prashant87/Self-Balancing-Robot-on-Tiva-C-TM4C-Dev-KIT/Mechanical/Robot Frame Base/Pin2s.SLDPRT

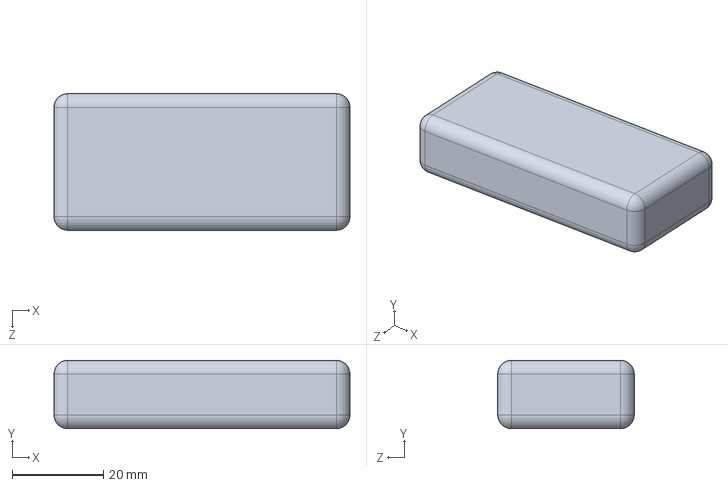
[picture p19: CAD file, 2020-07-25]
Mechanical/Robot Frame Base/Pin2s.SLDPRT
65.0 x 15.0 x 30.0 mm
