prashant87/Self-Balancing-Robot-on-Tiva-C-TM4C-Dev-KIT/Mechanical/Robot Frame Base/Mạch TT.SLDPRT

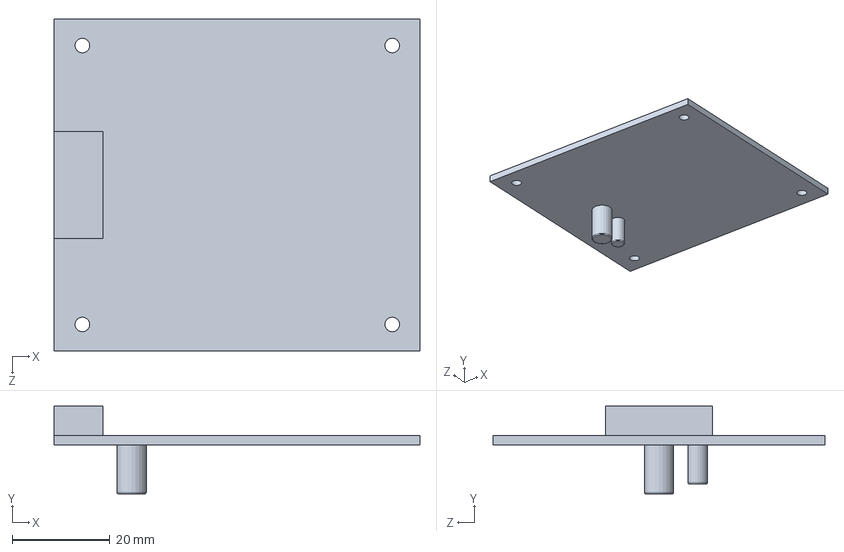
[picture p20: CAD file, 2020-07-25]
Mechanical/Robot Frame Base/Mạch TT.SLDPRT
75.0 x 18.0 x 68.0 mm
