prashant87/Self-Balancing-Robot-on-Tiva-C-TM4C-Dev-KIT/Mechanical/Robot Frame Base/Trụ6.SLDPRT

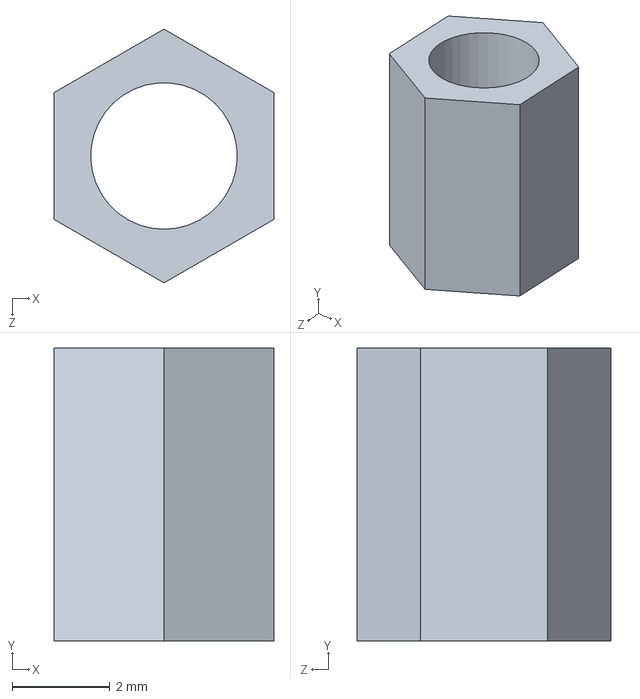
[picture p21: CAD file, 2020-07-25]
Mechanical/Robot Frame Base/Trụ6.SLDPRT
4.50 x 6.00 x 5.20 mm
