prashant87/Self-Balancing-Robot-on-Tiva-C-TM4C-Dev-KIT/Mechanical/Robot Frame Base/Bánh xe.SLDPRT

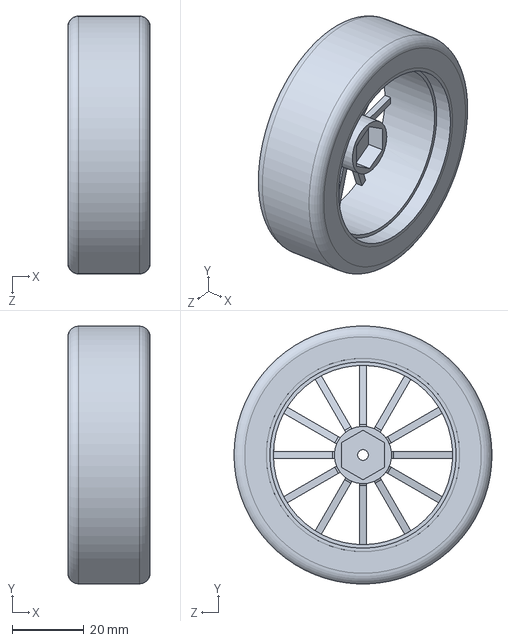
[picture p22: CAD file, 2020-07-25]
Mechanical/Robot Frame Base/Bánh xe.SLDPRT
23.0 x 71.9 x 72.0 mm
