prashant87/Self-Balancing-Robot-on-Tiva-C-TM4C-Dev-KIT/Mechanical/Robot Frame Base/Base4.SLDPRT

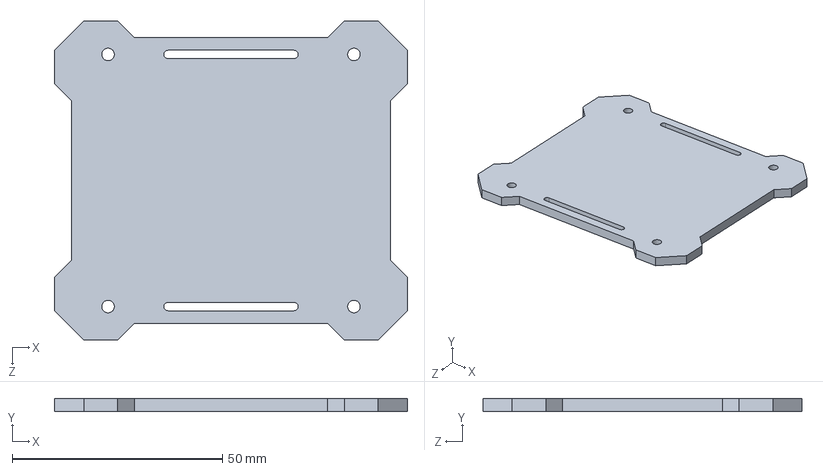
[picture p23: CAD file, 2020-07-25]
Mechanical/Robot Frame Base/Base4.SLDPRT
84.0 x 3.00 x 76.0 mm
