prashant87/Self-Balancing-Robot-on-Tiva-C-TM4C-Dev-KIT/Mechanical/Robot Frame Base/Cầu H.SLDPRT

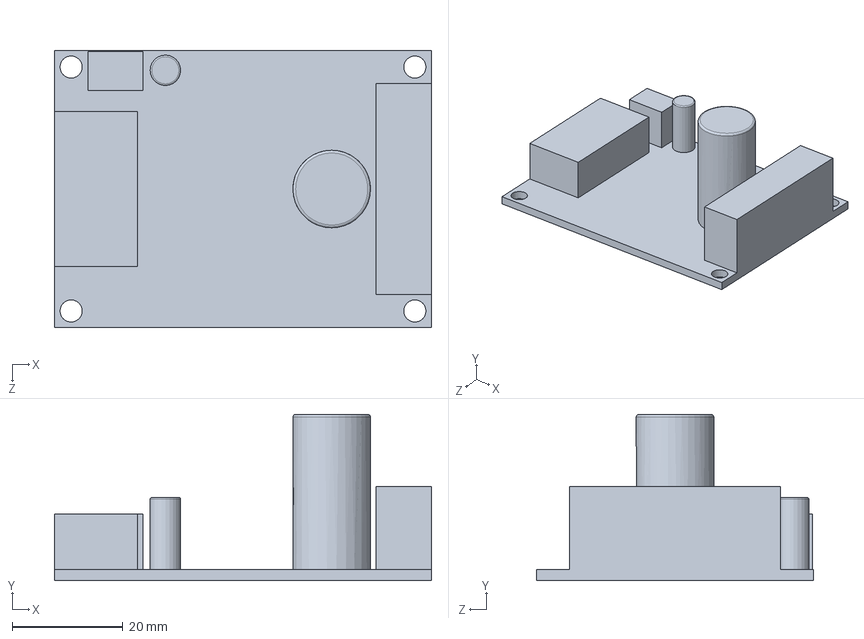
[picture p24: CAD file, 2020-07-25]
Mechanical/Robot Frame Base/Cầu H.SLDPRT
68.0 x 30.0 x 50.0 mm
