prashant87/Self-Balancing-Robot-on-Tiva-C-TM4C-Dev-KIT/Mechanical/Robot Frame Base/IMU_Quick.SLDPRT

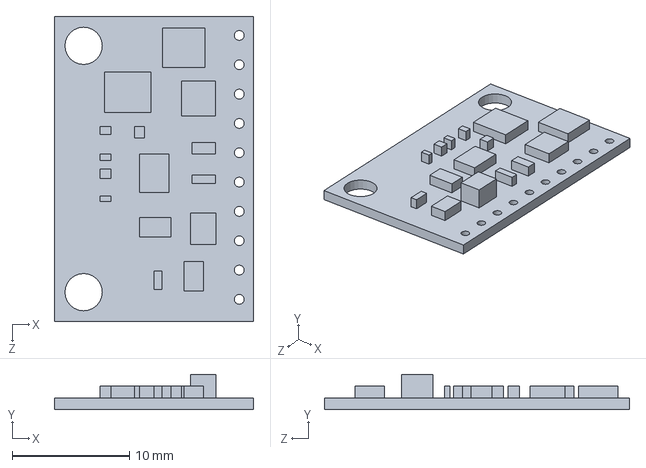
[picture p25: CAD file, 2020-07-25]
Mechanical/Robot Frame Base/IMU_Quick.SLDPRT
17.0 x 3.00 x 26.0 mm
