prashant87/Self-Balancing-Robot-on-Tiva-C-TM4C-Dev-KIT/Mechanical/Robot Frame Base/Nối trục ĐC.SLDPRT

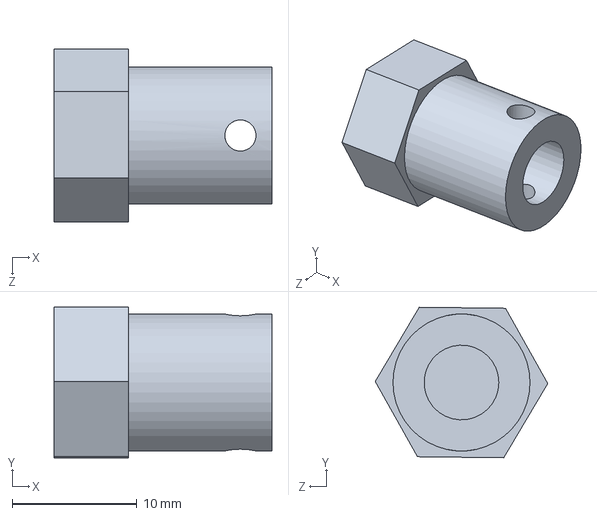
[picture p26: CAD file, 2020-07-25]
Mechanical/Robot Frame Base/Nối trục ĐC.SLDPRT
17.5 x 12.1 x 13.9 mm
