prashant87/Self-Balancing-Robot-on-Tiva-C-TM4C-Dev-KIT/Mechanical/Robot Frame Base/MạchBoost.SLDPRT

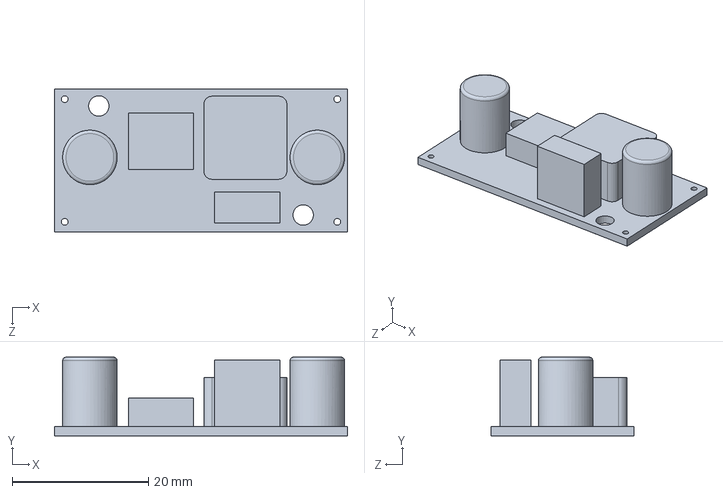
[picture p27: CAD file, 2020-07-25]
Mechanical/Robot Frame Base/MạchBoost.SLDPRT
43.0 x 11.6 x 21.0 mm
