prashant87/Self-Balancing-Robot-on-Tiva-C-TM4C-Dev-KIT/Mechanical/Robot Frame Base/Base1.SLDPRT

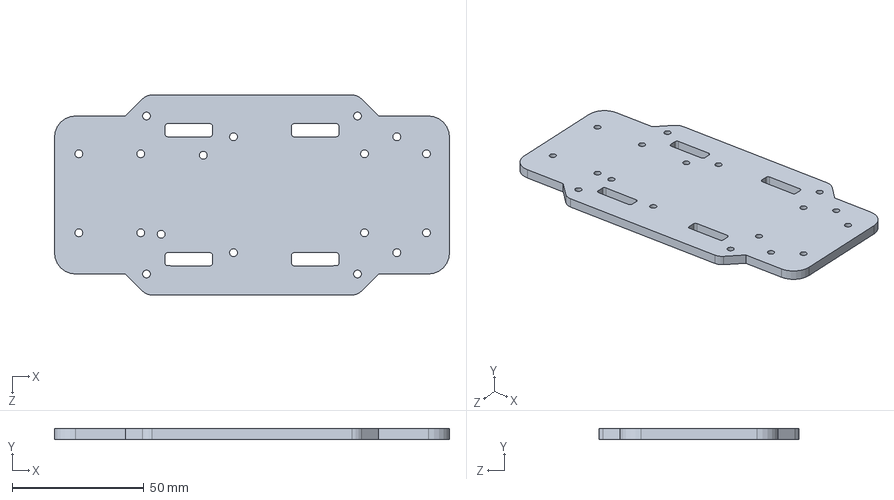
[picture p28: CAD file, 2020-07-25]
Mechanical/Robot Frame Base/Base1.SLDPRT
150.0 x 4.00 x 76.0 mm
