prashant87/Self-Balancing-Robot-on-Tiva-C-TM4C-Dev-KIT/Firmware/Tiva C with RTOS/Application/TwoWheel/twowheel.c

#include "FreeRTOS.h"
#include "timers.h"
#include "pid/pid.h"
#include "debug.h"
#include "motor_control/motor_control.h"
#include "drivers/MPU6050.h"
#include "drivers/pwm.h"
pid_t PID;
static TimerHandle_t xTimersAngleBase;

float a_get[2];
float a_out[2];
void twowheel_service_control_loop(TimerHandle_t xTimer)
{

    MPU6050_Complimentary_Angle(a_get);

    a_out[LEFT]=pid_compute_2(&PID,- a_get[0] ,MOVEBASE_PERIOD_MS);
    a_out[RIGHT]= a_out[LEFT];

    motor_set(a_out);

    DBG("A: %d \n",(int)a_get[0]);
}


xStatusTypeDef twowheel_service_control_init(void)
{
    PID = (pid_t)
        {
            .kp=10,
            .ki=01,
            .kd=0.0,//0.006
            .Ts=0.001
        };
    xTimersAngleBase = xTimerCreate("Angle base", 1, pdTRUE, ( void * ) 0, twowheel_service_control_loop);


    return OK;
}
xStatusTypeDef twowheel_service_control_start(void)
{
    xTimerStart( xTimersAngleBase, 0 );
    HBrigdeEnable(LEFT, ON);
        HBrigdeEnable(RIGHT,ON);
    return OK;

}
