prashant87/Self-Balancing-Robot-on-Tiva-C-TM4C-Dev-KIT/Firmware/Tiva C with RTOS/Application/motor_control/motor_control.h

#ifndef  MOTOR_CONTROL_H_
#define  MOTOR_CONTROL_H_
#define MOVEBASE_PERIOD_MS          20

#include "debug.h"
xStatusTypeDef motor_control_serivce_init(void);
xStatusTypeDef motor_control_service_start(void);
xStatusTypeDef motor_set(float w[2]);

#endif
