prashant87/Self-Balancing-Robot-on-Tiva-C-TM4C-Dev-KIT/Firmware/Tiva C non OS/QEI/QEI.h

/*
 * QEI.h
 *
 *  Created on: Jul 31, 2018
 *      Author: rockm
 */

#ifndef QEI_QEI_H_
#define QEI_QEI_H_

extern void QEIL_Init(void);
extern void QEIR_Init(void);
extern double QEIVeloGet_left(void);
extern double QEIVeloGet_right(void);




#endif /* QEI_QEI_H_ */
