prashant87/Self-Balancing-Robot-on-Tiva-C-TM4C-Dev-KIT/Firmware/Tiva C non OS/MPU/MPU6050.h

/*
 * MPU6050.h
 *
 *  Created on: Jun 29, 2017
 *      Author: minht57
 */

#ifndef MPU6050_MPU6050_H_
#define MPU6050_MPU6050_H_

#ifdef __cplusplus
extern "C" {
#endif

//            |         SCL/PA6|------->
//            |         SDA/PA7|------->

#define FREQ_UPDATE         100  //Hz

#define MPU6050_I2C                 SYSCTL_PERIPH_I2C1
#define MPU6050_I2C_GPIO            SYSCTL_PERIPH_GPIOA
#define MPU6050_I2C_SCL             GPIO_PA6_I2C1SCL
#define MPU6050_I2C_SDA             GPIO_PA7_I2C1SDA
#define MPU6050_I2C_GPIO_BASE       GPIO_PORTA_BASE
#define MPU6050_GPIO_SCL            GPIO_PIN_6
#define MPU6050_GPIO_SDA            GPIO_PIN_7
#define MPU6050_I2C_BASE            I2C1_BASE

#define MPU6050_TIMER               SYSCTL_PERIPH_TIMER0
#define MPU6050_TIMER_BASE          TIMER0_BASE
#define MPU6050_TIMER_BASE_TIMER    TIMER_A
#define MPU6050_TIMER_INT           INT_TIMER0A
#define MPU6050_TIMER_CONFIG        TIMER_CFG_PERIODIC
#define MPU6050_TIMER_INT_FLAGS     TIMER_TIMA_TIMEOUT

void MPU6050_Init(void);
void MPU6050_Get_Accel_Raw(int16_t * bufData);
void MPU6050_Get_Gyro_Raw(int16_t * bufData);
void MPU6050_Kalman_Angle(double * d_angle);//ham lay gia tri goc sau khi loc Kalman
void MPU6050_Complimentary_Angle(double * d_angle);//ham lay gia tri goc sau khi loc Bu
void Kalman_Filter_Process(void);
float ahrs_get_roll();

float ahrs_get_pitch();
float ahrs_get_yaw();

#ifdef __cplusplus
}
#endif

#endif /* MPU6050_MPU6050_H_ */
